wilyarti/esp32RadioAlarmClockPublic/src/alarm_functions.h

//
// Created by wilyarti on 13/9/25.
//

#ifndef ESP32RADIOALARMCLOCK_ALARM_FUNCTIONS_H
#define ESP32RADIOALARMCLOCK_ALARM_FUNCTIONS_H

#include "globals.h"

void incrementAlarmHours() ;
void incrementAlarmMinutes();
#endif //ESP32RADIOALARMCLOCK_ALARM_FUNCTIONS_H
