wilyarti/esp32RadioAlarmClockPublic/src/handleNewMessages.h

//
// Created by wilyarti on 12/9/25.
//
#pragma once
#include <UniversalTelegramBot.h>

#include "audio_functions.h"
#include "wifi_functions.h"

#ifndef ESP32RADIOALARMCLOCK_HANDLENEWMESSAGES_H
#define ESP32RADIOALARMCLOCK_HANDLENEWMESSAGES_H



void handleNewMessages(int numNewMessages);

#endif //ESP32RADIOALARMCLOCK_HANDLENEWMESSAGES_H
