wilyarti/esp32RadioAlarmClockPublic/src/serial_functions.h

#ifndef SERIAL_FUNCTIONS_H
#define SERIAL_FUNCTIONS_H
#pragma once
#include "main.h"
#include <Arduino.h>
#include <Arduino.h>
#include "commands.h"
#include "storage_functions.h"
#include "display.h"

//====================================================================================
//                                  Definitions
//====================================================================================
#define PIXEL_TIMEOUT 100     // 100ms Time-out between pixel requests
#define START_TIMEOUT 10000   // 10s Maximum time to wait at start transfer

#define BITS_PER_PIXEL 16     // 24 for RGB colour format, 16 for 565 colour format

// File names must be alpha-numeric characters (0-9, a-z, A-Z) or "/" underscore "_"
// other ascii characters are stripped out by client, including / generates
// sub-directories
#define DEFAULT_FILENAME "tft_screenshots/screenshot" // In case none is specified
#define FILE_TYPE "png"       // jpg, bmp, png, tif are valid

// Filename extension
// '#' = add incrementing number, '@' = add timestamp, '%' add millis() timestamp,
// '*' = add nothing
// '@' and '%' will generate new unique filenames, so beware of cluttering up your
// hard drive with lots of images! The PC client sketch is set to limit the number of
// saved images to 1000 and will then prompt for a restart.
#define FILE_EXT  '@'

// Number of pixels to send in a burst (minimum of 1), no benefit above 8
// NPIXELS values and render times:
// NPIXELS 1 = use readPixel() = >5s and 16-bit pixels only
// NPIXELS >1 using rectRead() 2 = 1.75s, 4 = 1.68s, 8 = 1.67s
#define NPIXELS 8  // Must be integer division of both TFT width and TFT height

//====================================================================================

bool serialScreenServer(String filename);
void sendParameters(String filename);
void checkSerial();
void setupNetworkViaInput();
#endif
